therebelrobot/cyberdeck-2026/circuits/wio-LR1121-breakout/layer-bottom.png

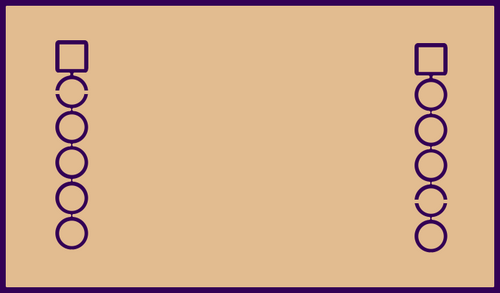
circuits/wio-LR1121-breakout/layer-bottom.png
