therebelrobot/cyberdeck-2026/circuits/wio-LR1121-breakout/silkscreen-top.png

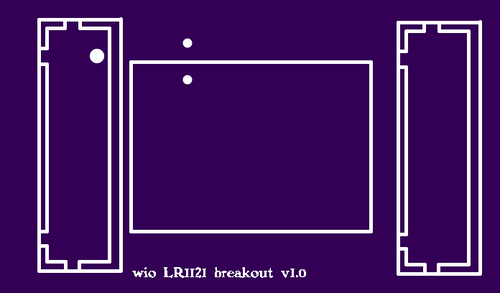
circuits/wio-LR1121-breakout/silkscreen-top.png
