therebelrobot/cyberdeck-2026/circuits/wio-LR1121-breakout/soldermask-top.png

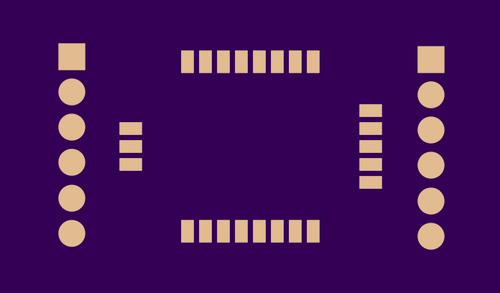
circuits/wio-LR1121-breakout/soldermask-top.png
