therebelrobot/cyberdeck-2026/wiring/end-to-end-wiring.png

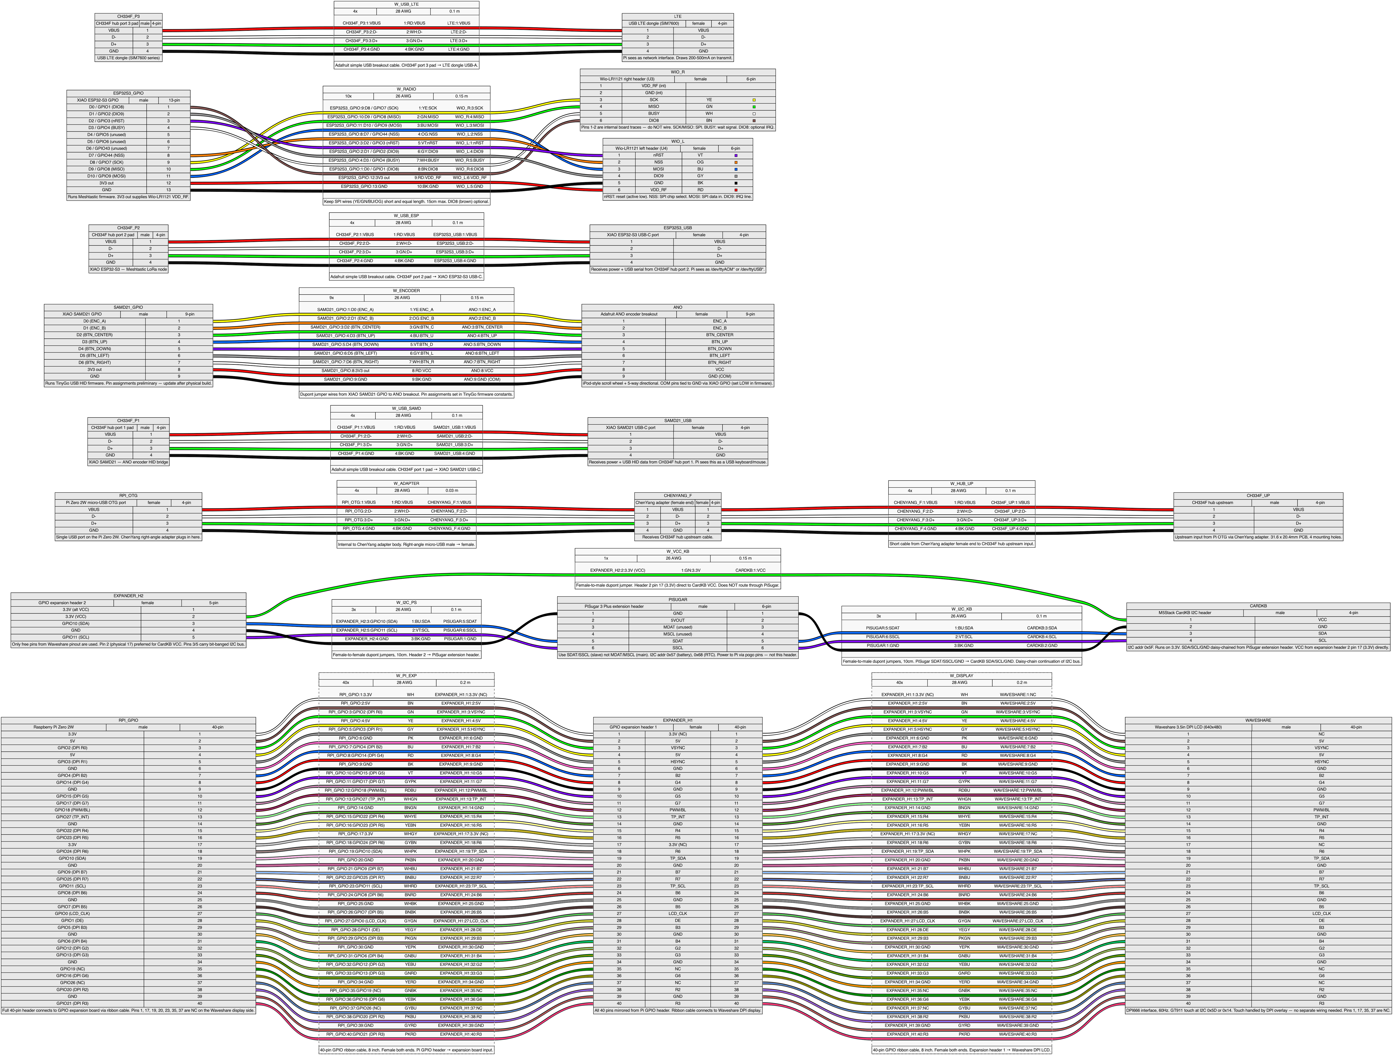
wiring/end-to-end-wiring.png
