therebelrobot/cyberdeck-2026/wiring/wio-lr1121-xiao-esp32s3-harness/wio-lr1121-xiao-esp32s3-harness.png

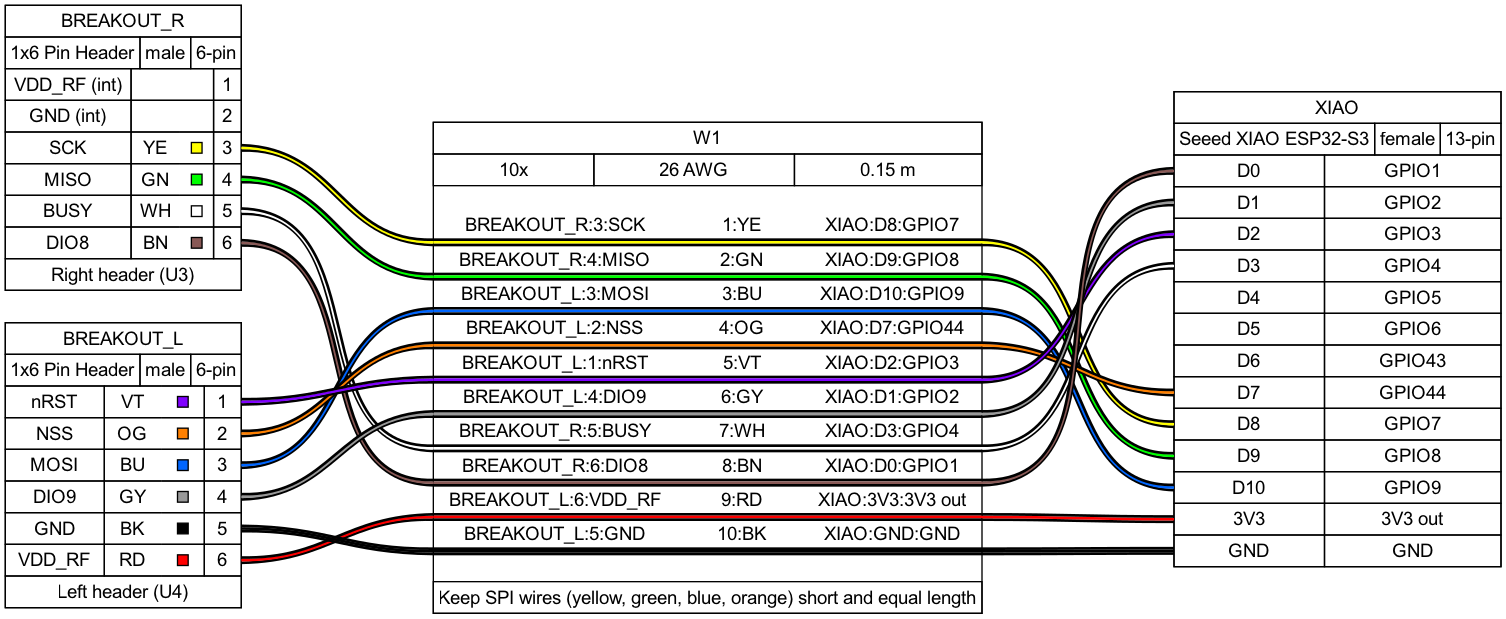
wiring/wio-lr1121-xiao-esp32s3-harness/wio-lr1121-xiao-esp32s3-harness.png
